sstojos/zynthian-miniature/other-info/openscad/all-in-one-pcb.jpg

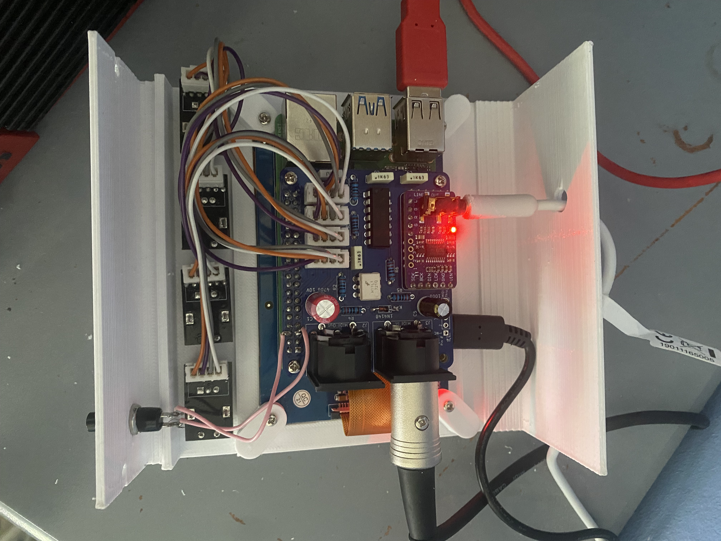
other-info/openscad/all-in-one-pcb.jpg
