sstojos/zynthian-miniature/other-info/PCB-main-without-MIDI-PCB-connectors.png

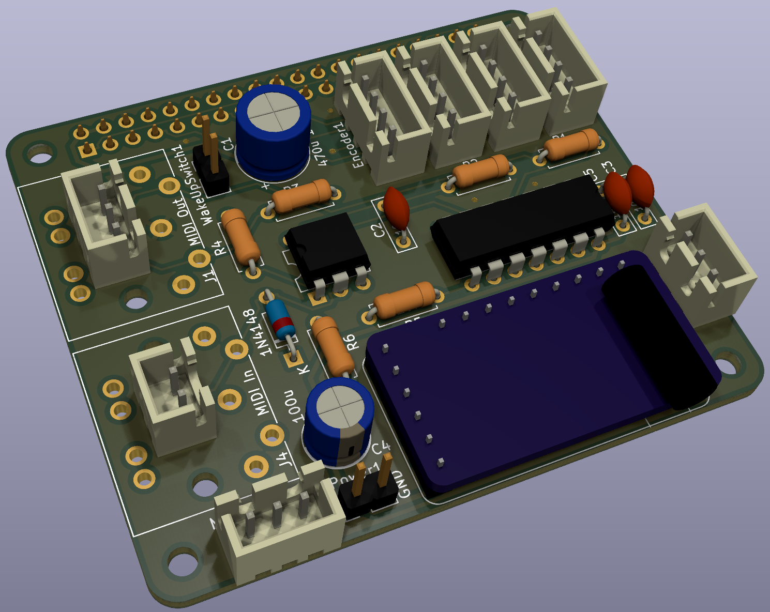
other-info/PCB-main-without-MIDI-PCB-connectors.png
